transportkollektiv/lora-wifi-location-tracker/src/config.sample.h

#include <stdint.h>

#define CFG_eu868 1
#define CFG_sx1276_radio 1

// This EUI must be in little-endian format, so least-significant-byte
// first. When copying an EUI from ttnctl output, this means to reverse
// the bytes.
static const uint8_t DEVEUI[8] = { 0x00, 0x00, 0x00, 0x00, 0x00, 0x00, 0x00, 0x00 };

// This should also be in little endian format, see above. (LSB)
static const uint8_t APPEUI[8] = { 0x00, 0x00, 0x00, 0x00, 0x00, 0x00, 0x00, 0x00 };

// This key should be in big endian format (MSB)
static const uint8_t APPKEY[16] = { 0x00, 0x00, 0x00, 0x00, 0x00, 0x00, 0x00, 0x00, 0x00, 0x00, 0x00, 0x00, 0x00, 0x00, 0x00, 0x00 };

// sleeptime in microseconds
static const unsigned int SLEEP_DURATION = 10 * 60 * 1000 * 1000;
